Meebleeps/MeeBleeps-Freaq-FM-Synth/src/pseudorandom2048_int8.h

/*
  pseudorandom2048_int8.h - defines a table to semi-random values with a slight smoothing between them

  used for the LFO/carrier/modulator 

  can be replaced with any values you like, but must be 2048 cells to match the other tables
*/

#ifndef PSEUDORANDOM2048_H_
#define PSEUDORANDOM2048_H_

#if ARDUINO >= 100
 #include "Arduino.h"
#else
 #include "WProgram.h"
#endif
#include "mozzi_pgmspace.h"

#define PSEUDORANDOM2048_NUM_CELLS 2048
#define PSEUDORANDOM2048_SAMPLERATE 2048

/** @ingroup tables
random table. smoothed
*/
CONSTTABLE_STORAGE(int8_t) PSEUDORANDOM2048_DATA [2048]  =
        {
            41,41,41,41,41,41,41,41,41,41,41,41,41,41,41,41
            ,41,41,41,41,41,41,41,41,41,41,41,41,41,41,41,41
            ,41,41,41,41,41,41,41,41,41,41,41,41,41,41,41,41
            ,35,29,24,18,12,6,0,-6,-11,-17,-23,-29,-35,-40,-46,-52
            ,-52,-52,-52,-52,-52,-52,-52,-52,-52,-52,-52,-52,-52,-52,-52,-52
            ,-52,-52,-52,-52,-52,-52,-52,-52,-52,-52,-52,-52,-52,-52,-52,-52
            ,-52,-52,-52,-52,-52,-52,-52,-52,-52,-52,-52,-52,-52,-52,-52,-52
            ,-52,-51,-51,-51,-50,-50,-50,-50,-49,-49,-49,-48,-48,-48,-47,-47
            ,-47,-47,-47,-47,-47,-47,-47,-47,-47,-47,-47,-47,-47,-47,-47,-47
            ,-47,-47,-47,-47,-47,-47,-47,-47,-47,-47,-47,-47,-47,-47,-47,-47
            ,-47,-47,-47,-47,-47,-47,-47,-47,-47,-47,-47,-47,-47,-47,-47,-47
            ,-47,-48,-48,-49,-49,-50,-50,-51,-51,-51,-52,-52,-53,-53,-54,-54
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
                ,-3,-3,-3,-3,-3,-3,-3,-3,-3,-3,-3,-3,-3,-3,-3,-3
                ,-3,-3,-3,-3,-3,-3,-3,-3,-3,-3,-3,-3,-3,-3,-3,-3
                ,-3,-3,-3,-3,-3,-3,-3,-3,-3,-3,-3,-3,-3,-3,-3,-3
                ,-3,-3,-3,-3,-3,-3,-3,-3,-3,-3,-3,-3,-3,-3,-3,-3
                ,11,11,11,11,11,11,11,11,11,11,11,11,11,11,11,11
                ,11,11,11,11,11,11,11,11,11,11,11,11,11,11,11,11
                ,11,11,11,11,11,11,11,11,11,11,11,11,11,11,11,11
                ,11,11,11,11,11,11,11,11,11,11,11,11,11,11,11,11
                ,56,56,56,56,56,56,56,56,56,56,56,56,56,56,56,56
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


        };
*/

#endif /* PSEUDORANDOM2048_H_ */
