Meebleeps/MeeBleeps-Freaq-FM-Synth/src/nullwaveform2048_int8.h

/*
  NULLWAVEFORM2018_int8.h - defines a table representing a zero waveform

  used to silence the oscillator 
    
  can be replaced with any values you like, but must be 2048 cells to match the other tables
*/
#ifndef NULLWAVEFORM2048_H_
#define NULLWAVEFORM2048_H_

#if ARDUINO >= 100
 #include "Arduino.h"
#else
 #include "WProgram.h"
#endif
#include "mozzi_pgmspace.h"

#define NULLWAVEFORM2048_NUM_CELLS 2048
#define NULLWAVEFORM2048_SAMPLERATE 2048

/** @ingroup tables
reverse saw table
*/

CONSTTABLE_STORAGE(int8_t) NULLWAVEFORM2048_DATA [2048]  =
        {
             0,0,0,0,0,0,0,0,0,0,0,0,0,0,0,0
            ,0,0,0,0,0,0,0,0,0,0,0,0,0,0,0,0
            ,0,0,0,0,0,0,0,0,0,0,0,0,0,0,0,0
            ,0,0,0,0,0,0,0,0,0,0,0,0,0,0,0,0
            ,0,0,0,0,0,0,0,0,0,0,0,0,0,0,0,0
            ,0,0,0,0,0,0,0,0,0,0,0,0,0,0,0,0
            ,0,0,0,0,0,0,0,0,0,0,0,0,0,0,0,0
            ,0,0,0,0,0,0,0,0,0,0,0,0,0,0,0,0
            ,0,0,0,0,0,0,0,0,0,0,0,0,0,0,0,0
            ,0,0,0,0,0,0,0,0,0,0,0,0,0,0,0,0
            ,0,0,0,0,0,0,0,0,0,0,0,0,0,0,0,0
            ,0,0,0,0,0,0,0,0,0,0,0,0,0,0,0,0
            ,0,0,0,0,0,0,0,0,0,0,0,0,0,0,0,0
            ,0,0,0,0,0,0,0,0,0,0,0,0,0,0,0,0
            ,0,0,0,0,0,0,0,0,0,0,0,0,0,0,0,0
            ,0,0,0,0,0,0,0,0,0,0,0,0,0,0,0,0
            ,0,0,0,0,0,0,0,0,0,0,0,0,0,0,0,0
            ,0,0,0,0,0,0,0,0,0,0,0,0,0,0,0,0
            ,0,0,0,0,0,0,0,0,0,0,0,0,0,0,0,0
            ,0,0,0,0,0,0,0,0,0,0,0,0,0,0,0,0
            ,0,0,0,0,0,0,0,0,0,0,0,0,0,0,0,0
            ,0,0,0,0,0,0,0,0,0,0,0,0,0,0,0,0
            ,0,0,0,0,0,0,0,0,0,0,0,0,0,0,0,0
            ,0,0,0,0,0,0,0,0,0,0,0,0,0,0,0,0
            ,0,0,0,0,0,0,0,0,0,0,0,0,0,0,0,0
            ,0,0,0,0,0,0,0,0,0,0,0,0,0,0,0,0
            ,0,0,0,0,0,0,0,0,0,0,0,0,0,0,0,0
            ,0,0,0,0,0,0,0,0,0,0,0,0,0,0,0,0
            ,0,0,0,0,0,0,0,0,0,0,0,0,0,0,0,0
            ,0,0,0,0,0,0,0,0,0,0,0,0,0,0,0,0
            ,0,0,0,0,0,0,0,0,0,0,0,0,0,0,0,0
            ,0,0,0,0,0,0,0,0,0,0,0,0,0,0,0,0
            ,0,0,0,0,0,0,0,0,0,0,0,0,0,0,0,0
            ,0,0,0,0,0,0,0,0,0,0,0,0,0,0,0,0
            ,0,0,0,0,0,0,0,0,0,0,0,0,0,0,0,0
            ,0,0,0,0,0,0,0,0,0,0,0,0,0,0,0,0
            ,0,0,0,0,0,0,0,0,0,0,0,0,0,0,0,0
            ,0,0,0,0,0,0,0,0,0,0,0,0,0,0,0,0
            ,0,0,0,0,0,0,0,0,0,0,0,0,0,0,0,0
            ,0,0,0,0,0,0,0,0,0,0,0,0,0,0,0,0
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
        };


#endif /* NULLWAVEFORM2048_H_ */
