Meebleeps/MeeBleeps-Freaq-FM-Synth/src/mutantBitmaps.h

/*----------------------------------------------------------------------------------------------------------
 * mutantBitmaps.h
 * 
 * defines bitmap icons for displaying on the LED matrix
 * 
 * Stored in prog mem - copy the values into RAM before using 
 * 
 * Source Code Repository:  https://github.com/Meebleeps/MeeBleeps-Freaq-FM-Synth
 * Youtube Channel:         https://www.youtube.com/channel/UC4I1ExnOpH_GjNtm7ZdWeWA
 * 
 * (C) 2021-2022 Meebleeps
*-----------------------------------------------------------------------------------------------------------
*/
#ifndef MUTANT_BITMAPS
#define MUTANT_BITMAPS
#include <avr/pgmspace.h>
#include <Arduino.h>

#include "MutantFMSynthOptions.h"

const PROGMEM byte BITMAP_MEEBLEEPS[]  = {B00011000,B01111110,B11011011,B11011011,B11011011,B11011011,B11000011,B00000110};

const PROGMEM byte BITMAP_NUMERALS[8][8]  = {
                                       {B00000000,B00000000,B00000000,B11100000,B10100000,B10100000,B10100000,B11100111}
                                      ,{B00000000,B00000000,B00000000,B01000000,B01000000,B01000000,B01000111,B01000000}
                                      ,{B00000000,B00000000,B00000000,B11100000,B00100000,B11100111,B10000000,B11100000}
                                      ,{B00000000,B00000000,B00000000,B11100000,B00100111,B11100000,B00100000,B11100000}
                                      ,{B00000000,B00000000,B00000000,B10100111,B10100000,B11100000,B00100000,B00100000}
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
                                    ,{B00000000,B00000000,B00000000,B00000001,B00000110,B00011000,B01100000,B10000000}
                                    ,{B00000000,B00000000,B00000000,B11111111,B00000000,B00000000,B00000000,B00000000}
                                    };

#endif
